aki27kbd/picot5400/images/design/FFC_01.jpg

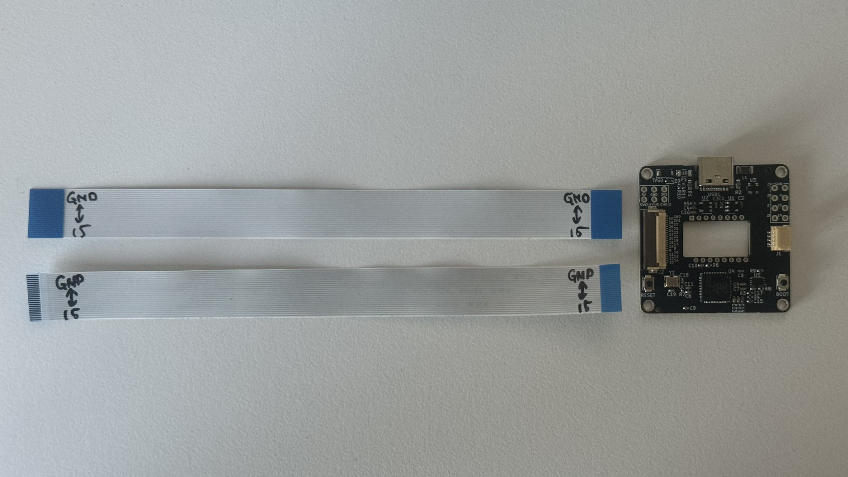
images/design/FFC_01.jpg
