aki27kbd/picot5400/images/gallery_01.jpg

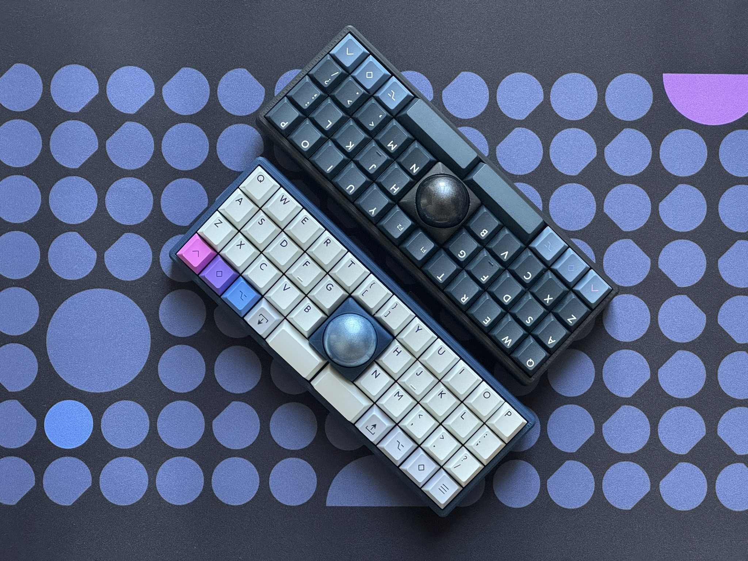
images/gallery_01.jpg
